sibiryakov/maria-phono-preamp/drawings/3d pcb render.png

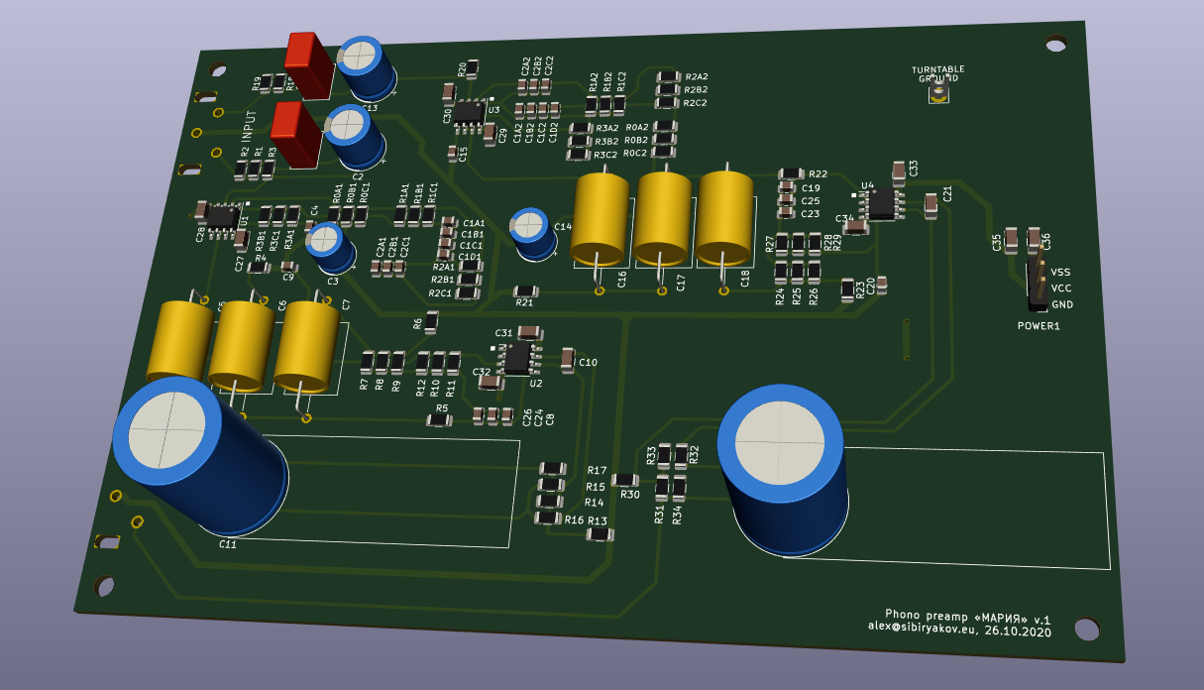
drawings/3d pcb render.png
