sibiryakov/maria-phono-preamp/drawings/two_cases1.JPG

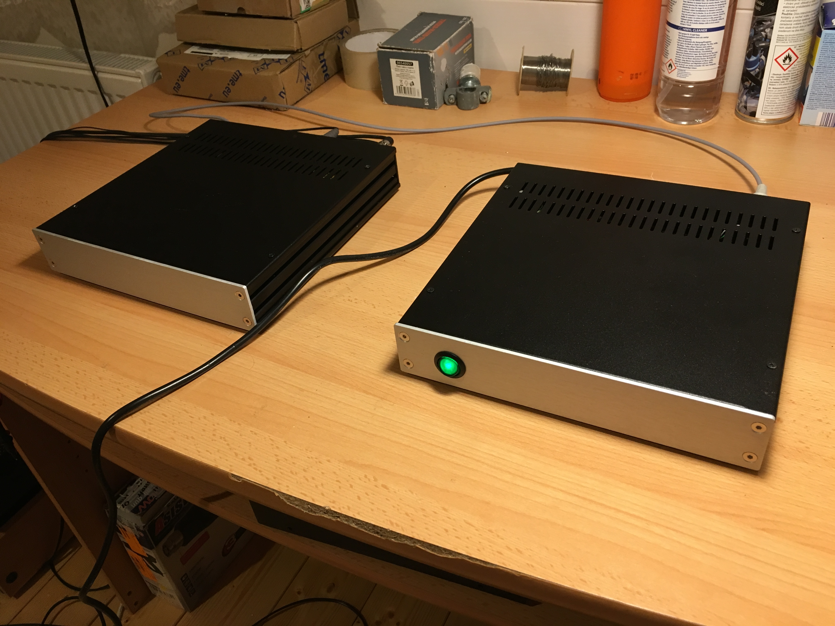
drawings/two_cases1.JPG
